mathrax-s/ishinokoe_ws/Stone_Sensor_v2/wavetable.h

// sin
static const int8_t sin_wave[] = {
  0, 0, 1, 2, 3, 4, 5, 6, 7, 8, 9, 10, 11, 12, 13, 14,
  15, 16, 17, 18, 19, 20, 21, 22, 23, 24, 25, 26, 27, 28, 29, 30,
  31, 32, 33, 34, 35, 36, 37, 38, 39, 39, 40, 41, 42, 43, 44, 45,
  46, 47, 48, 49, 50, 51, 52, 52, 53, 54, 55, 56, 57, 58, 59, 60,
  60, 61, 62, 63, 64, 65, 66, 66, 67, 68, 69, 70, 71, 71, 72, 73,
  74, 75, 75, 76, 77, 78, 79, 79, 80, 81, 82, 82, 83, 84, 85, 85,
  86, 87, 88, 88, 89, 90, 90, 91, 92, 92, 93, 94, 94, 95, 96, 96,
  97, 98, 98, 99, 99, 100, 101, 101, 102, 102, 103, 104, 104, 105, 105, 106,
  106, 107, 107, 108, 108, 109, 109, 110, 110, 111, 111, 112, 112, 113, 113, 114,
  114, 115, 115, 115, 116, 116, 117, 117, 117, 118, 118, 118, 119, 119, 119, 120,
  120, 120, 121, 121, 121, 122, 122, 122, 122, 123, 123, 123, 123, 123, 124, 124,
  124, 124, 124, 125, 125, 125, 125, 125, 125, 126, 126, 126, 126, 126, 126, 126,
  126, 126, 126, 126, 126, 126, 126, 126, 126, 127, 126, 126, 126, 126, 126, 126,
  126, 126, 126, 126, 126, 126, 126, 126, 126, 126, 125, 125, 125, 125, 125, 125,
  124, 124, 124, 124, 124, 123, 123, 123, 123, 123, 122, 122, 122, 122, 121, 121,
  121, 120, 120, 120, 119, 119, 119, 118, 118, 118, 117, 117, 117, 116, 116, 115,
  115, 115, 114, 114, 113, 113, 112, 112, 111, 111, 110, 110, 109, 109, 108, 108,
  107, 107, 106, 106, 105, 105, 104, 104, 103, 102, 102, 101, 101, 100, 99, 99,
  98, 98, 97, 96, 96, 95, 94, 94, 93, 92, 92, 91, 90, 90, 89, 88,
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
  11032, 11688, 12383, 13119, 13899, 14726, 15601, 16529, 17512, 18553, 19656, 20825,
  22064, 23376, 24766, 26238, 27798, 29451, 31203, 33058, 35024, 37106, 39313, 41650,
  44127, 46751, 49531, 52476, 55597, 58903, 62405, 0
};
