mathrax-s/ishinokoe_ws/Stone_Sensor_v2/pitches.h

/* 
 * File:   pitches.h
 * Author: MATHRAX
 *
 * Created on 2013/06/11, 18:23
 */

#ifndef PITCHES_H
#define  PITCHES_H

/*************************************************
 * Public Constants
 *************************************************/
#define NOTE_C0     0
#define NOTE_Db0  1
#define NOTE_D0     2
#define NOTE_Eb0  3
#define NOTE_E0     4
#define NOTE_F0     5
#define NOTE_Gb0  6
#define NOTE_G0     7
#define NOTE_Ab0  8
#define NOTE_A0     9
#define NOTE_Bb0  10
#define NOTE_B0     11
#define NOTE_C1     12
#define NOTE_Db1  13
#define NOTE_D1     14
#define NOTE_Eb1  15
#define NOTE_E1     16
#define NOTE_F1     17
#define NOTE_Gb1  18
#define NOTE_G1     19
#define NOTE_Ab1  20
#define NOTE_A1     21
#define NOTE_Bb1  22
#define NOTE_B1     23
#define NOTE_C2     24
#define NOTE_Db2  25
#define NOTE_D2     26
#define NOTE_Eb2  27
#define NOTE_E2     28
#define NOTE_F2     29
#define NOTE_Gb2  30
#define NOTE_G2     31
#define NOTE_Ab2  32
#define NOTE_A2     33
#define NOTE_Bb2  34
#define NOTE_B2     35
#define NOTE_C3     36
#define NOTE_Db3  37
#define NOTE_D3     38
#define NOTE_Eb3  39
#define NOTE_E3     40
#define NOTE_F3     41
#define NOTE_Gb3  42
#define NOTE_G3     43
#define NOTE_Ab3  44
#define NOTE_A3     45
#define NOTE_Bb3  46
#define NOTE_B3     47
#define NOTE_C4     48
#define NOTE_Db4  49
#define NOTE_D4     50
#define NOTE_Eb4  51
#define NOTE_E4     52
#define NOTE_F4     53
#define NOTE_Gb4  54
#define NOTE_G4     55
#define NOTE_Ab4  56
#define NOTE_A4     57
#define NOTE_Bb4  58
#define NOTE_B4     59
#define NOTE_C5     60
#define NOTE_Db5  61
#define NOTE_D5     62
#define NOTE_Eb5  63
#define NOTE_E5     64
#define NOTE_F5     65
#define NOTE_Gb5  66
#define NOTE_G5     67
#define NOTE_Ab5  68
#define NOTE_A5     69
#define NOTE_Bb5  70
#define NOTE_B5     71
#define NOTE_C6     72
#define NOTE_Db6  73
#define NOTE_D6     74
#define NOTE_Eb6  75
#define NOTE_E6     76
#define NOTE_F6     77
#define NOTE_Gb6  78
#define NOTE_G6     79
#define NOTE_Ab6  80
#define NOTE_A6     81
#define NOTE_Bb6  82
#define NOTE_B6     83
#define NOTE_C7     84
#define NOTE_Db7  85
#define NOTE_D7     86
#define NOTE_Eb7  87
#define NOTE_E7     88
#define NOTE_F7     89
#define NOTE_Gb7  90
#define NOTE_G7     91
#define NOTE_Ab7  92
#define NOTE_A7     93
#define NOTE_Bb7  94
#define NOTE_B7     95
#define NOTE_C8     96
#define NOTE_Db8  97
#define NOTE_D8     98
#define NOTE_Eb8  99
#define NOTE_E8     100
#define NOTE_F8     101
#define NOTE_Gb8  102
#define NOTE_G8     103
#define NOTE_Ab8  104
#define NOTE_A8     105
#define NOTE_Bb8  106
#define NOTE_B8     107
#define NOTE_C9     108
#define NOTE_Db9  109
#define NOTE_D9     110
#define NOTE_Eb9  111
#define NOTE_E9     112
#define NOTE_F9     113
#define NOTE_Gb9  114
#define NOTE_G9     115
#define NOTE_Ab9  116
#define NOTE_A9     117
#define NOTE_Bb9  118
#define NOTE_B9     119
#define NOTE_C10  120
#define NOTE_Db10 121
#define NOTE_D10  122
#define NOTE_Eb10 123
#define NOTE_E10  124
#define NOTE_F10  125
#define NOTE_Gb10 126
#define NOTE_G10  127
#define NOTE_Ab10 128
#define NOTE_A10  129
#define NOTE_Bb10 130
#define NOTE_B10  131


#endif  /* PITCHES_H */
